ringotf/pico_gg_lcd/pics/diy hdmi examples.jpg

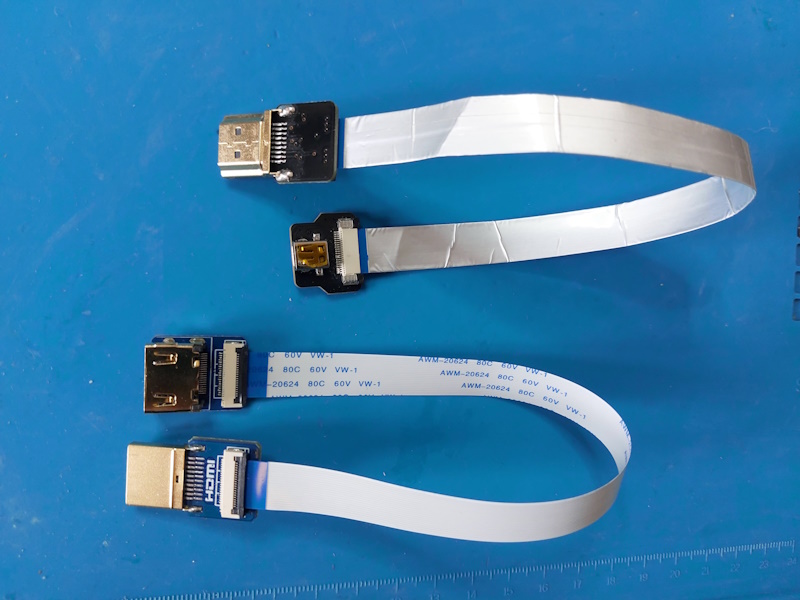
pics/diy hdmi examples.jpg
