ringotf/pico_gg_lcd/pics/proto3-2.png

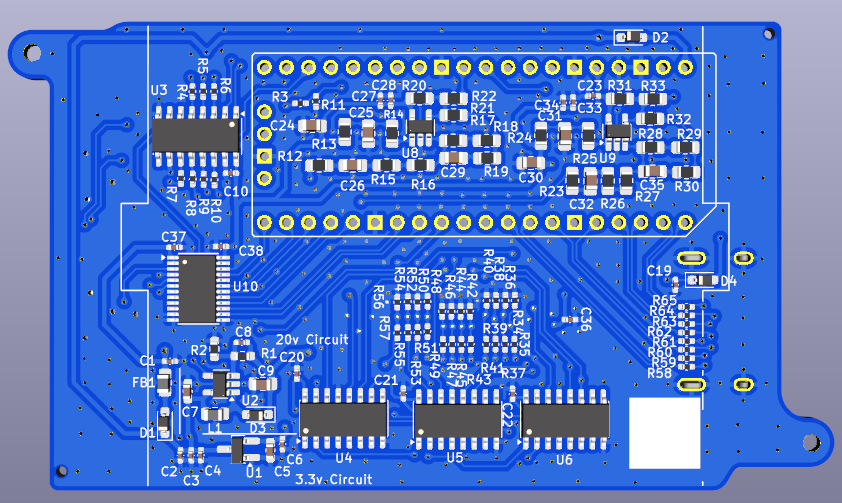
pics/proto3-2.png
