ringotf/pico_gg_lcd/pics/proto3-3.png

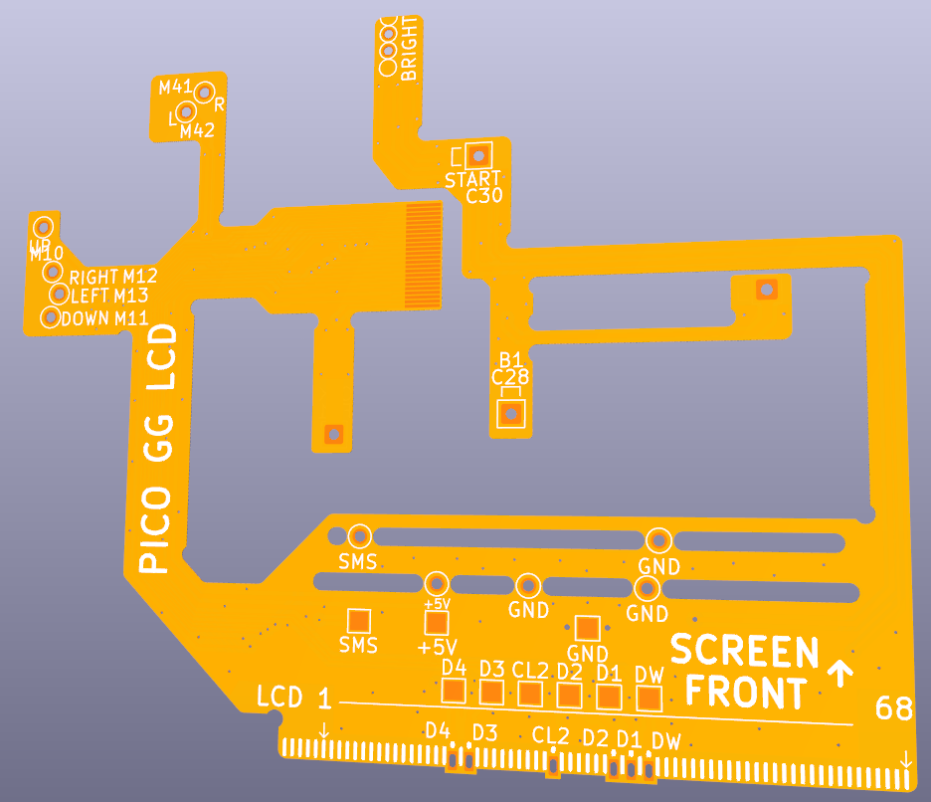
pics/proto3-3.png
