ringotf/pico_gg_lcd/pics/proto4-1.png

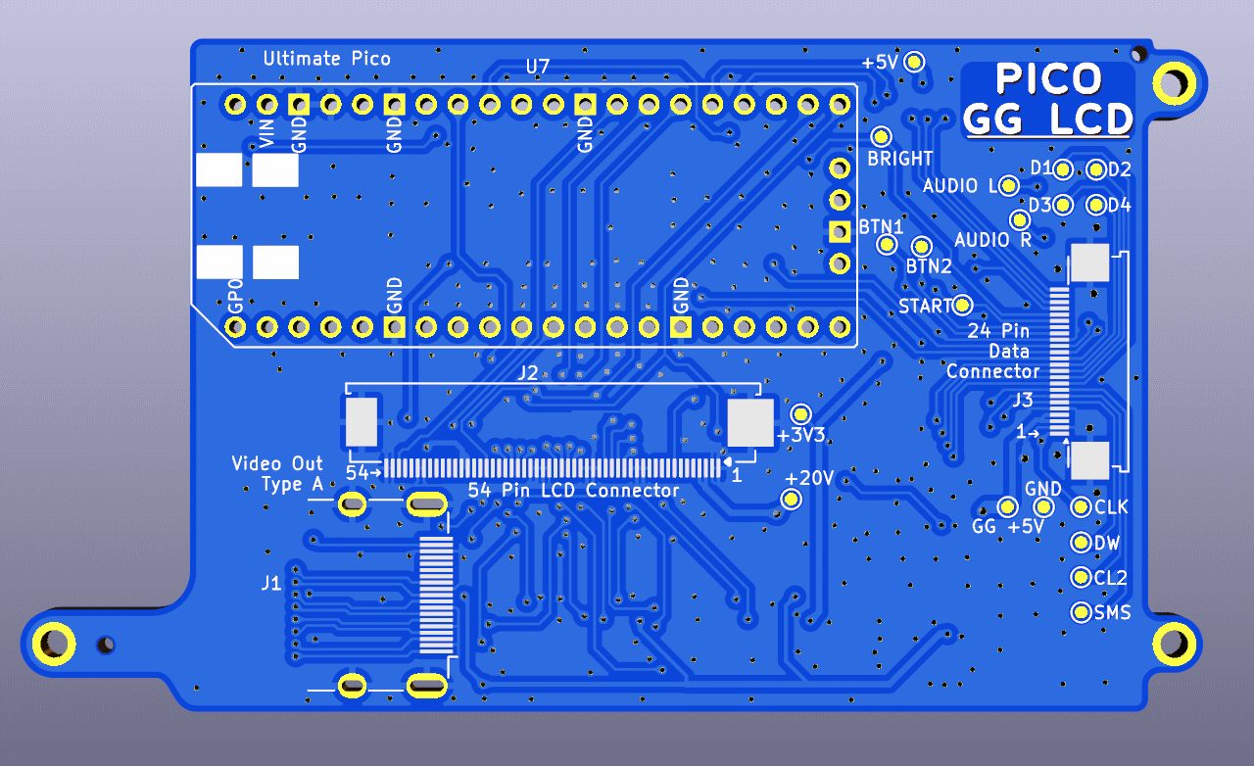
pics/proto4-1.png
