ringotf/pico_gg_lcd/pics/proto4-2.png

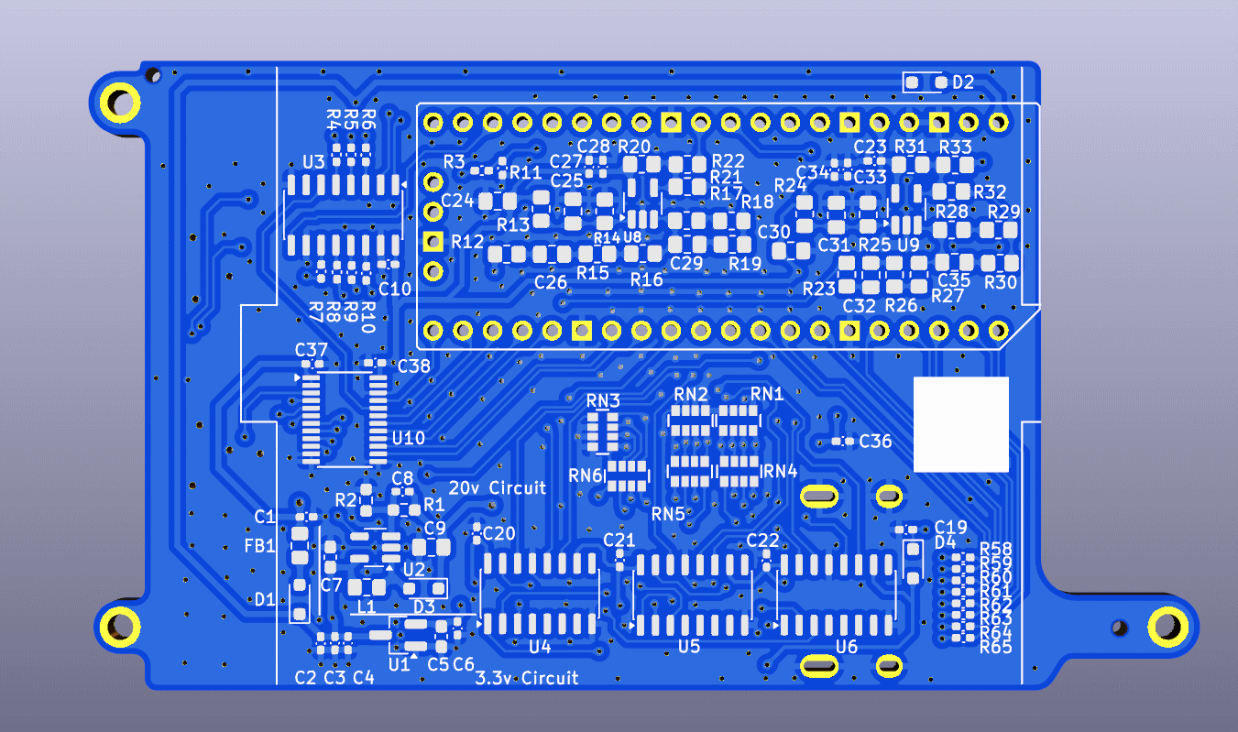
pics/proto4-2.png
