ringotf/pico_gg_lcd/pics/proto4-3.png

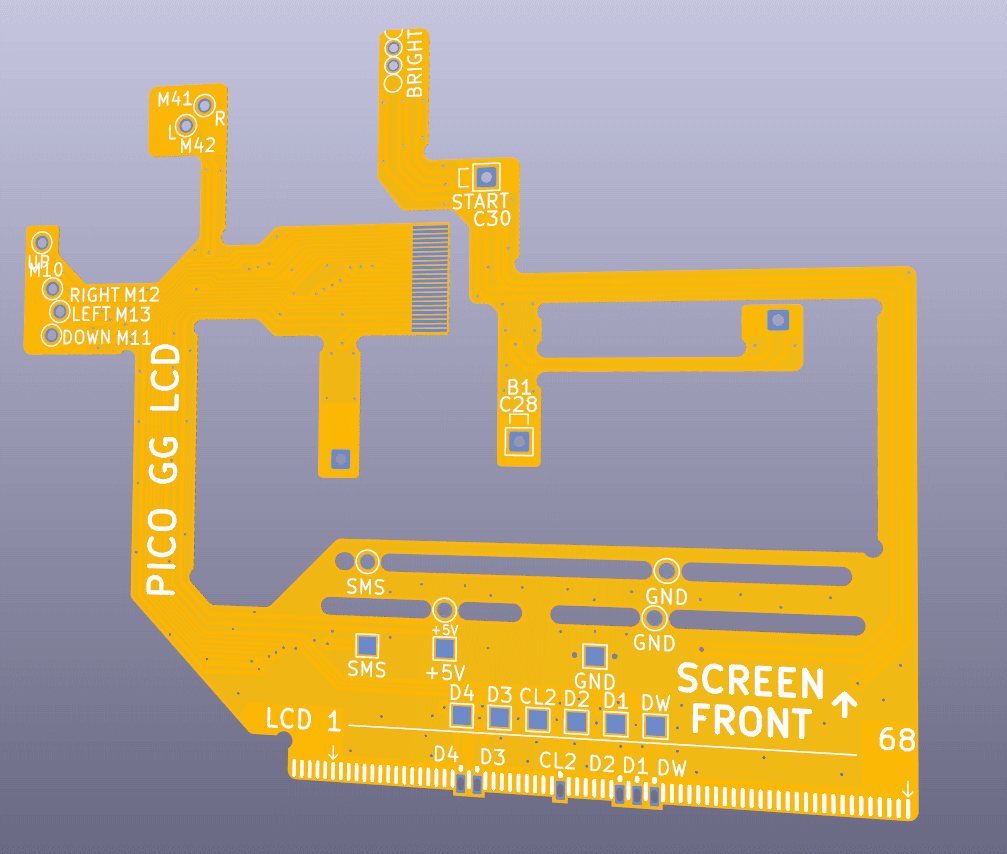
pics/proto4-3.png
