ringotf/pico_gg_lcd/pics/proto4-7.png

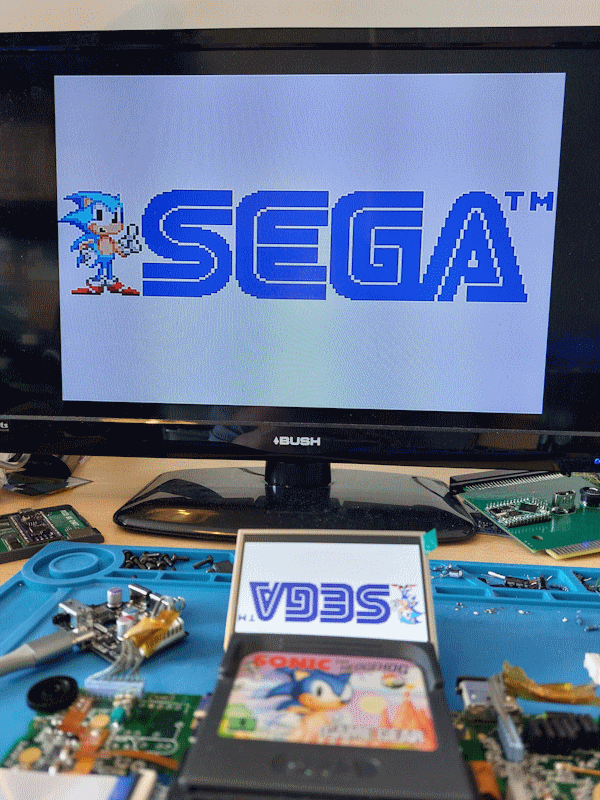
pics/proto4-7.png
