ringotf/pico_gg_lcd/pics/proto4-14.png

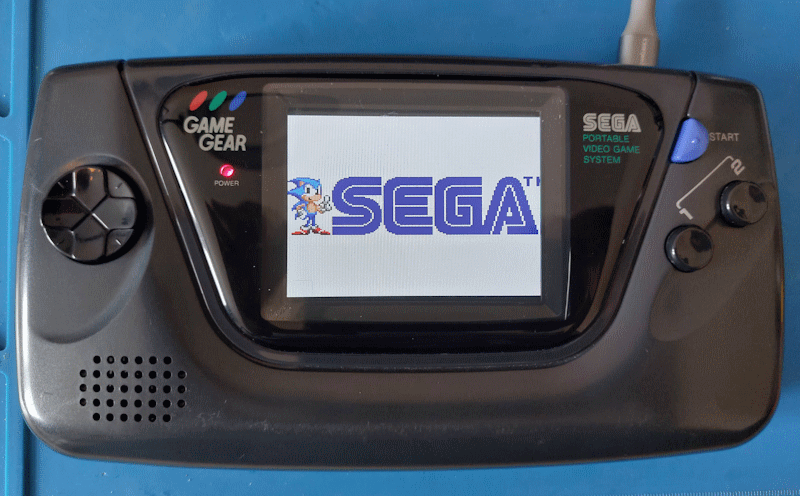
pics/proto4-14.png
