ringotf/pico_gg_lcd/pics/proto4-16.png

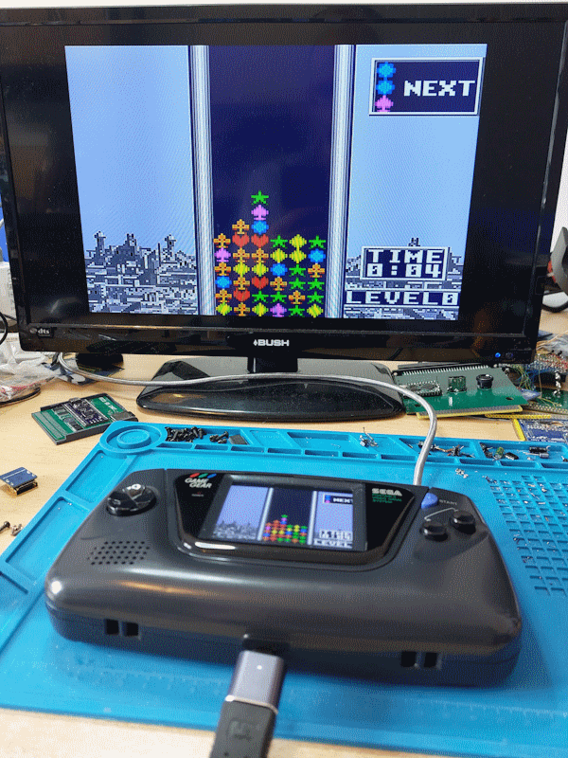
pics/proto4-16.png
