ringotf/pico_gg_lcd/pics/build1c.png

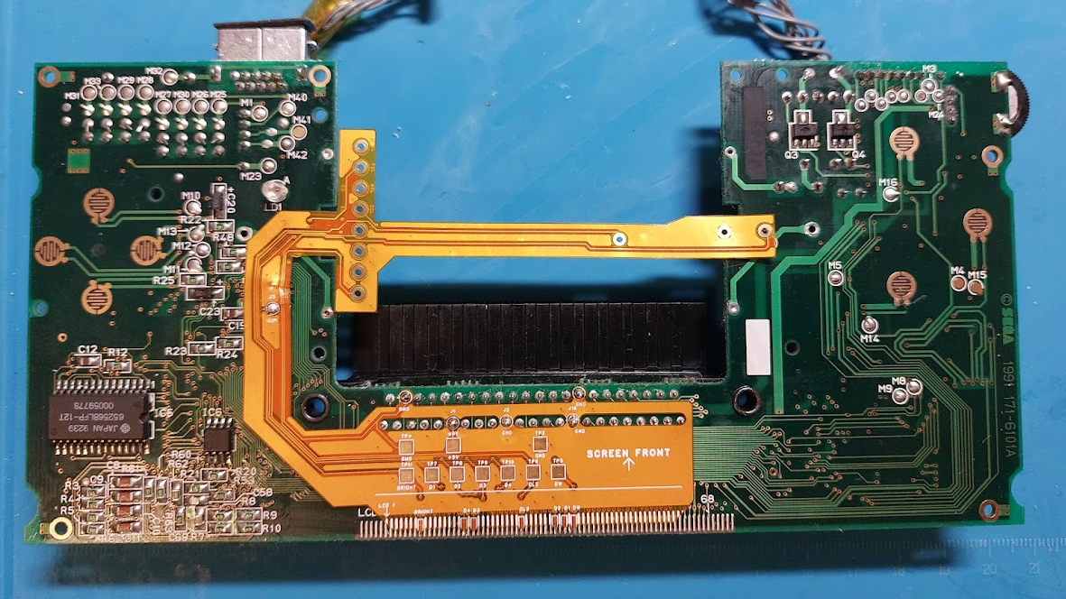
pics/build1c.png
